Kairuihu2903/SeniorDesign_BrailleBoard/Images/Screenshot 2023-12-29 at 12.18.16 AM.png

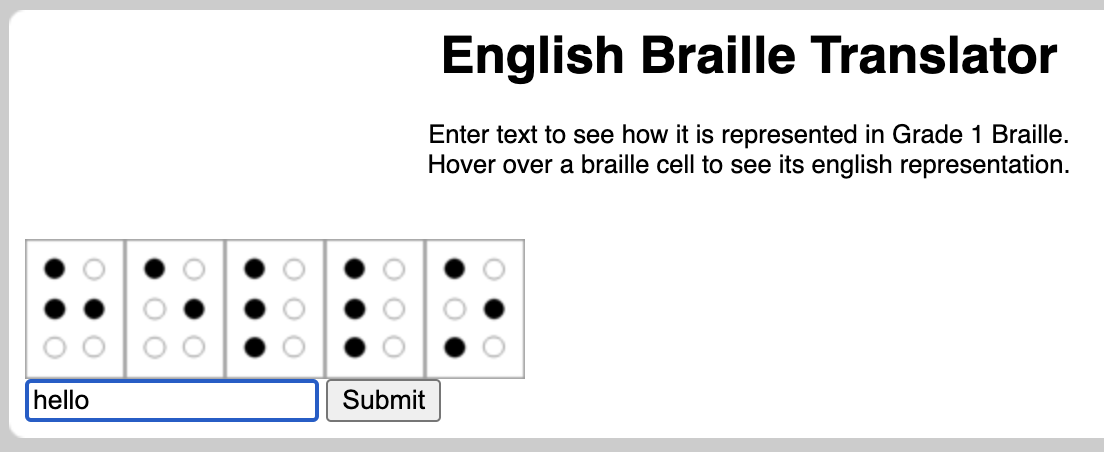
Images/Screenshot 2023-12-29 at 12.18.16 AM.png
