Kairuihu2903/SeniorDesign_BrailleBoard/Images/Screenshot 2023-12-29 at 12.27.56 AM.png

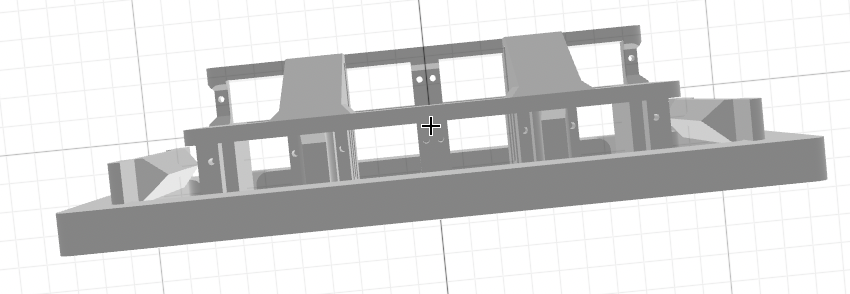
Images/Screenshot 2023-12-29 at 12.27.56 AM.png
