Kairuihu2903/SeniorDesign_BrailleBoard/Images/IMG_3354.jpg

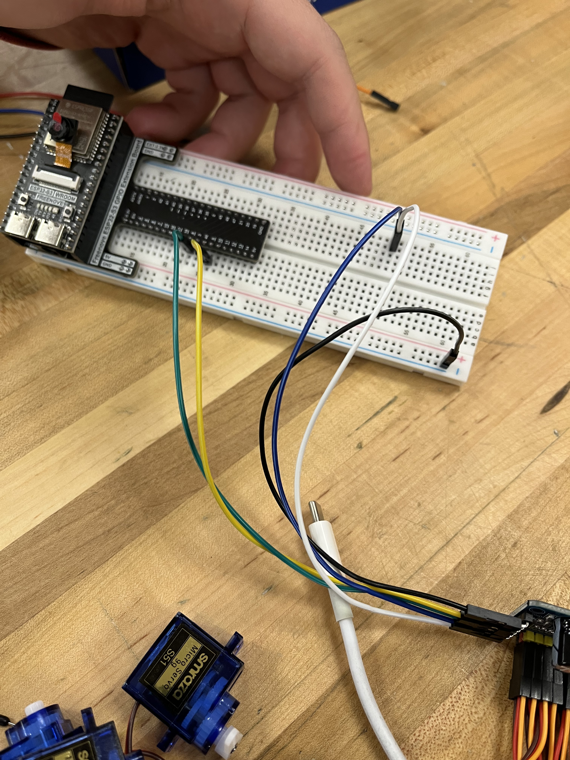
Images/IMG_3354.jpg
